OpenTransat/OpenTransat-Navigator/software/main/declination.h

/*
  declination.h - Magnetic declination with lat/lng resolution of 5 degrees and 1 byte range according to the World Magnetic Model 2015-2020
  declination is calculated at time: 2019.5
*/

#define NUM_LAT 35
#define NUM_LNG 73

//declination[i*NUM_LNG + j] returns magnetic declination at GPS [lat, lng] = [i*5 - 85, j*5 - 180]
const int8_t declination[35*73] PROGMEM = {
  127, 127, 127, 125, 120, 114, 109, 104, 99, 94, 89, 84, 80, 75, 70, 66, 61, 57, 52, 48, 44, 39, 35, 30, 26, 22, 18, 13, 9, 5, 0, -4, -8, -13, -17, -22, -26, -31, -35, -40, -44, -49, -54, -58, -63, -68, -73, -78, -83, -88, -93, -98, -103, -109, -114, -119, -125, -128, -128, -128, -128, -128, -128, -128, -128, -128, 127, 127, 127, 127, 127, 127, 127,
  127, 123, 117, 112, 106, 101, 96, 91, 87, 82, 78, 74, 69, 65, 61, 57, 53, 50, 46, 42, 38, 34, 30, 27, 23, 19, 15, 12, 8, 4, 0, -3, -7, -11, -15, -19, -23, -27, -31, -36, -40, -44, -49, -53, -58, -62, -67, -72, -76, -81, -86, -91, -97, -102, -107, -113, -119, -124, -128, -128, -128, -128, -128, -128, -128, -128, 127, 127, 127, 127, 127, 127, 127,
  111, 104, 99, 94, 89, 85, 81, 77, 73, 70, 66, 63, 60, 56, 53, 50, 47, 43, 40, 36, 33, 30, 26, 23, 20, 16, 13, 10, 6, 3, 0, -3, -7, -10, -14, -18, -21, -25, -29, -33, -37, -41, -46, -50, -54, -59, -63, -67, -72, -76, -81, -86, -90, -95, -100, -106, -111, -117, -124, -128, -128, -128, -128, -128, -128, 127, 127, 127, 127, 127, 125, 117, 111,
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
};
